import-tiago/Two-Trees-Bluer-3D-Printer/3D Models/Phone + Power Bank Table Stand/Phone + Power Bank (Flip Camera Version)-min.png

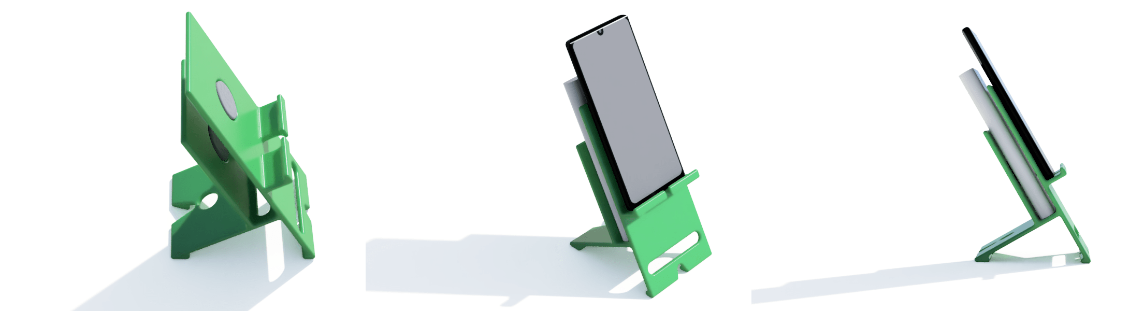
3D Models/Phone + Power Bank Table Stand/Phone + Power Bank (Flip Camera Version)-min.png
