import-tiago/Two-Trees-Bluer-3D-Printer/3D Models/Phone + Power Bank Table Stand/Phone + Power Bank (Induction Charging Version) (1)-min.jpg

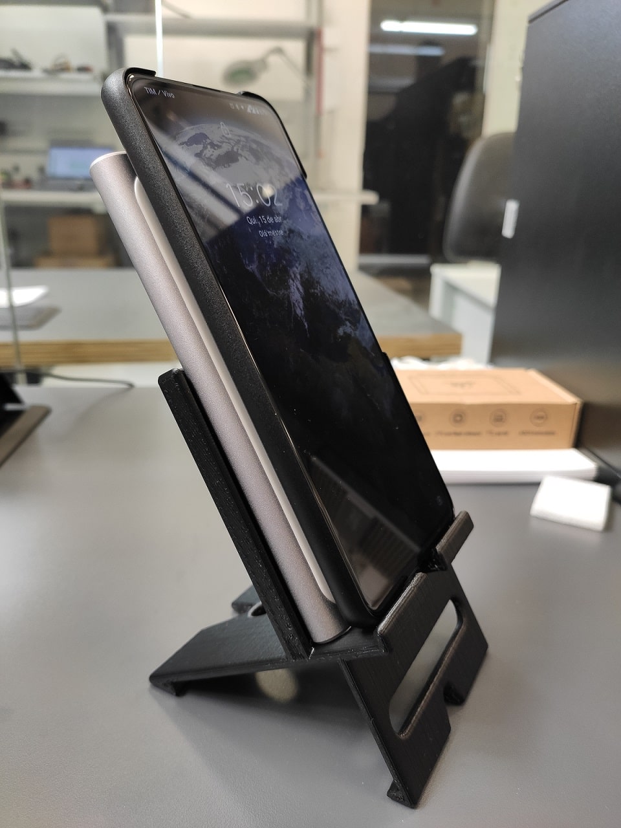
3D Models/Phone + Power Bank Table Stand/Phone + Power Bank (Induction Charging Version) (1)-min.jpg
