import-tiago/Two-Trees-Bluer-3D-Printer/3D Models/Phone + Power Bank Table Stand/Phone + Power Bank Stand (2)-min.jpg

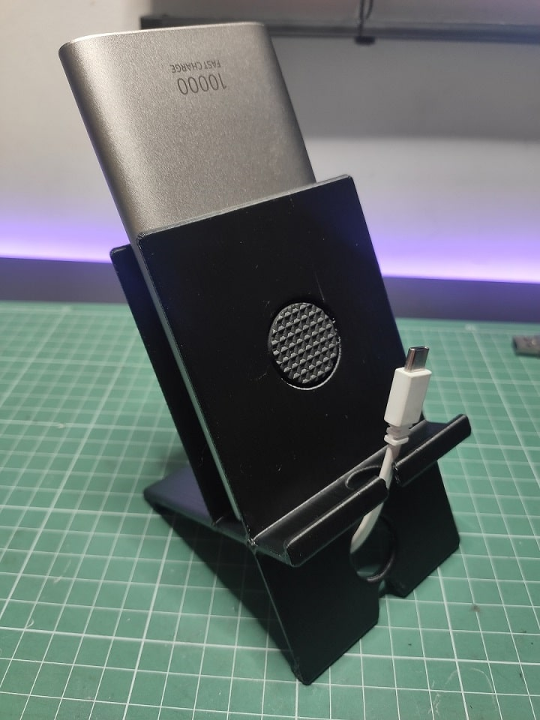
3D Models/Phone + Power Bank Table Stand/Phone + Power Bank Stand (2)-min.jpg
