import-tiago/Two-Trees-Bluer-3D-Printer/3D Models/Phone + Power Bank Table Stand/Phone + Power Bank Stand-min.png

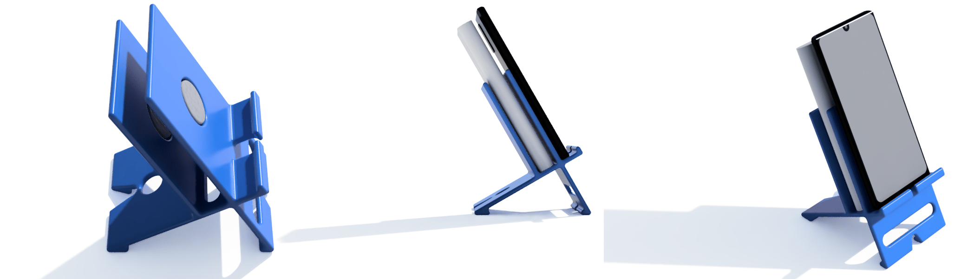
3D Models/Phone + Power Bank Table Stand/Phone + Power Bank Stand-min.png
