import-tiago/Two-Trees-Bluer-3D-Printer/Assets/IMG_20201112_212333.jpg

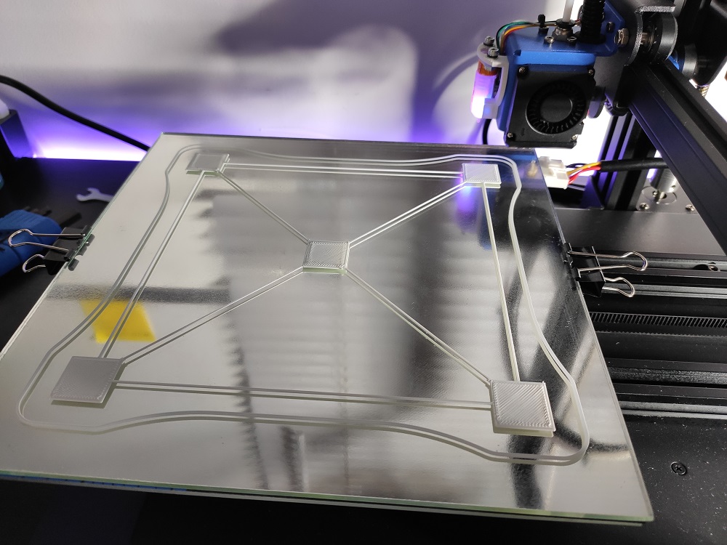
Assets/IMG_20201112_212333.jpg
