import-tiago/Two-Trees-Bluer-3D-Printer/Assets/IMG_20201114_103409.jpg

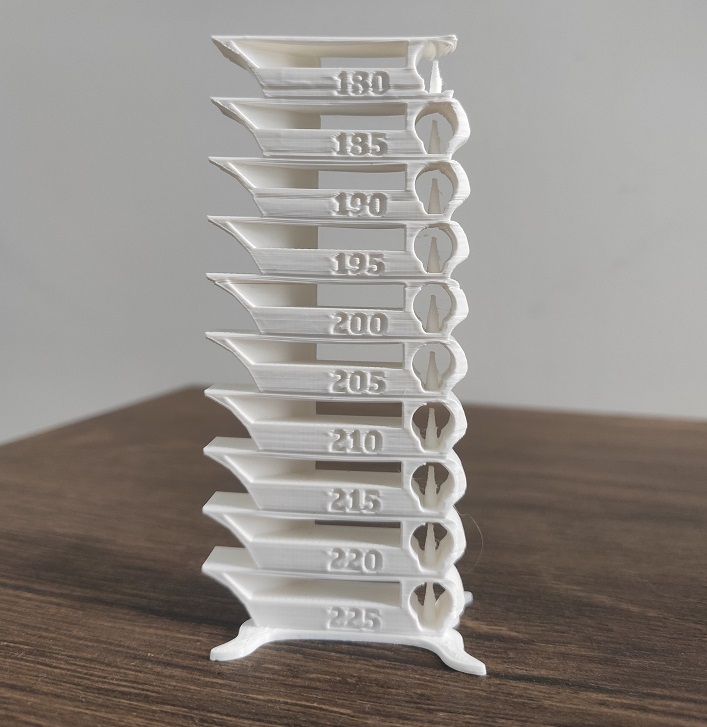
Assets/IMG_20201114_103409.jpg
